Mitchlol/Open-Pixel-Poi/Hardware/3D Printable Body/OldFiles/Open Pixel Poi - Shell - Round Diffused.3mf

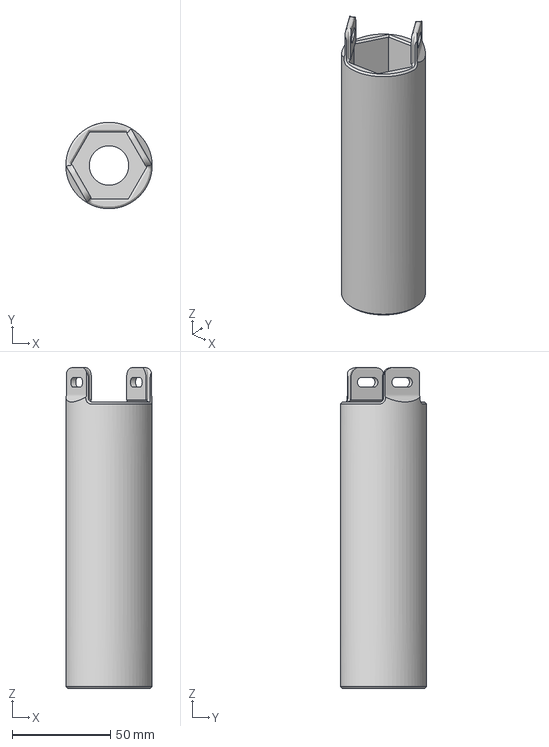
[picture p16: CAD file, 2026-07-14, an earlier design]
Hardware/3D Printable Body/OldFiles/Open Pixel Poi - Shell - Round Diffused.3mf
43.9 x 43.9 x 163.0 mm
